PittRocketryTeam/Airbrake-Computer/software/include/board.hpp

#ifndef BOARD_HPP
#define BOARD_HPP

// Defines pins and hardware configuration.

/**************************************************************************************************
 * Altimeter
 *************************************************************************************************/
#define ALTIMETER_SCL 19 
#define ALTIMETER_SDA 18
// Altimeter's default I2C address is 0x77

/**************************************************************************************************
 * IMU
 *************************************************************************************************/
#define IMU_ADDR 0X28

/**************************************************************************************************
 * Stepper motor 
 *************************************************************************************************/
#define M_DIR 31
#define M_STEP 30

#endif // BOARD_HPP 
